Diegoapp55/Proyecto-Sistemas-Embebidos-Smash-Rows/Esquematicos/ESP32/Smash Rows Back.png

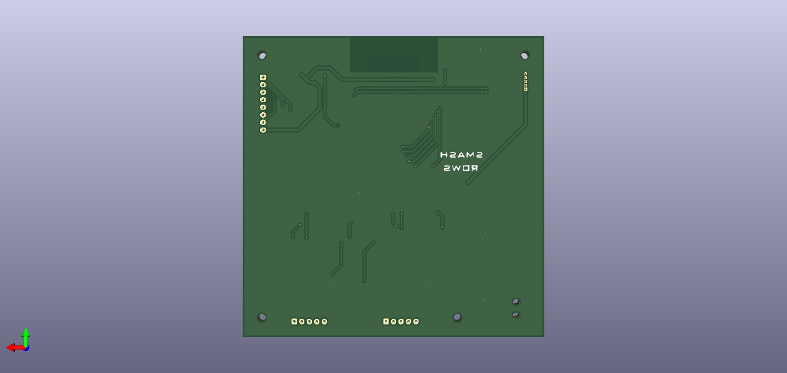
Esquematicos/ESP32/Smash Rows Back.png
