Diegoapp55/Proyecto-Sistemas-Embebidos-Smash-Rows/Imagenes/App_Image/AcercaDe.png

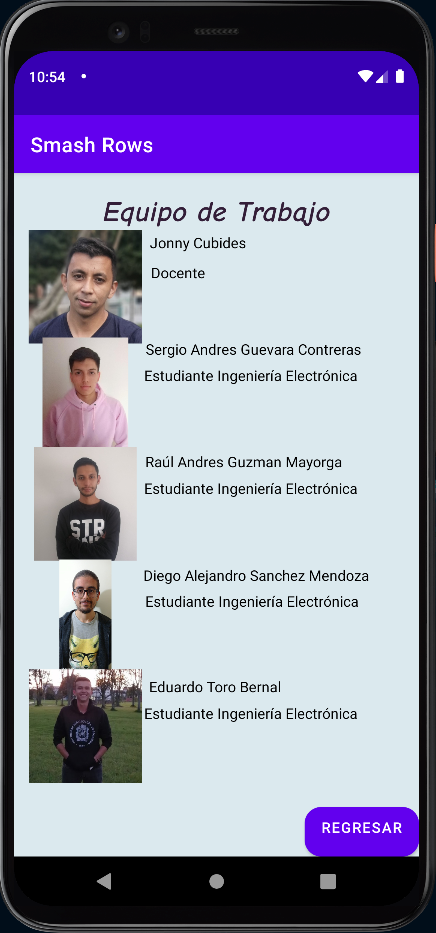
Imagenes/App_Image/AcercaDe.png
