Diegoapp55/Proyecto-Sistemas-Embebidos-Smash-Rows/Imagenes/App_Image/BaseDatos.png

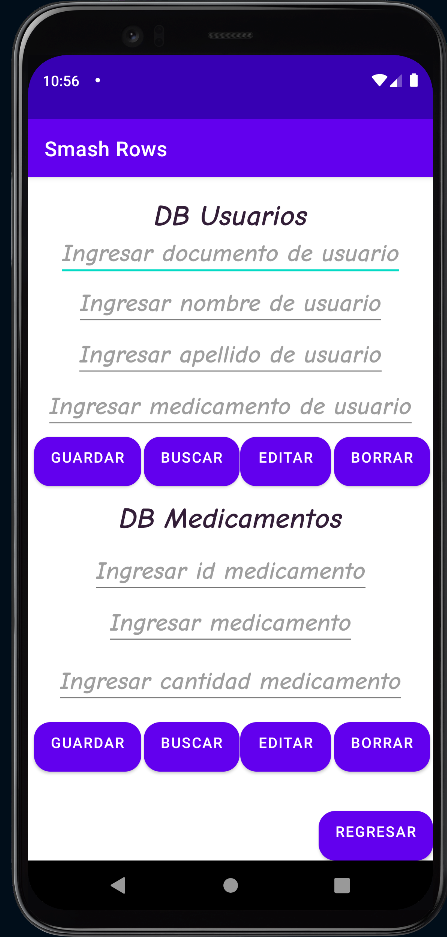
Imagenes/App_Image/BaseDatos.png
