Diegoapp55/Proyecto-Sistemas-Embebidos-Smash-Rows/Imagenes/App_Image/EscanearDocumento.png

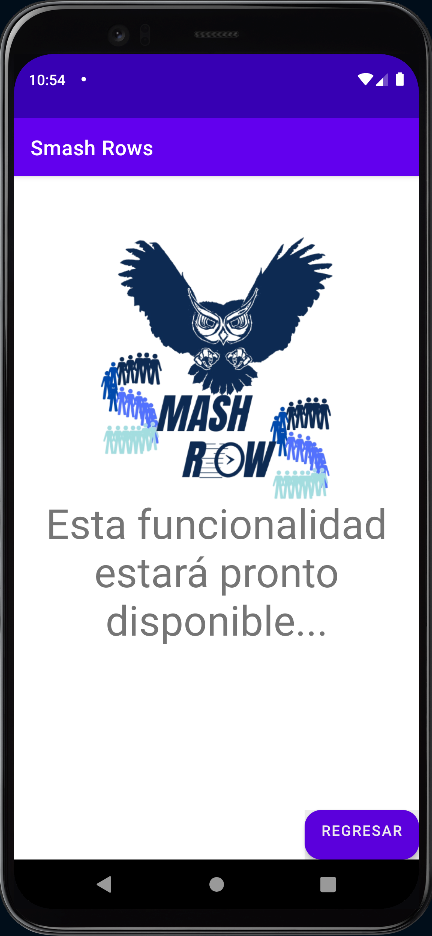
Imagenes/App_Image/EscanearDocumento.png
