Diegoapp55/Proyecto-Sistemas-Embebidos-Smash-Rows/Imagenes/App_Image/Insertar_Documento.png

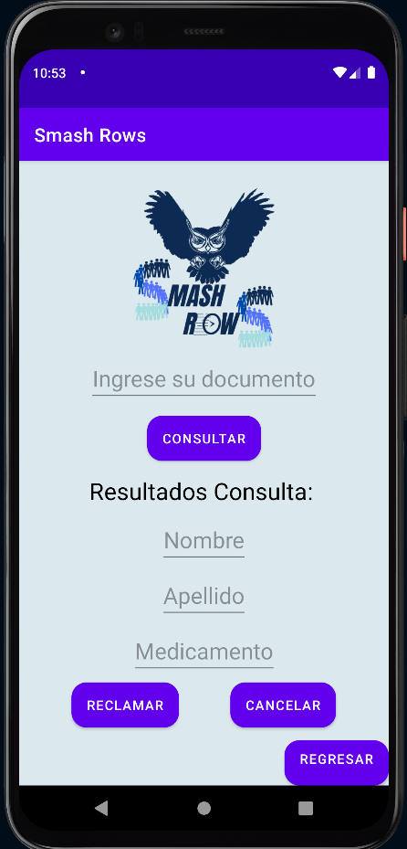
Imagenes/App_Image/Insertar_Documento.png
