Diegoapp55/Proyecto-Sistemas-Embebidos-Smash-Rows/Imagenes/App_Image/Interfaz_Principal.png

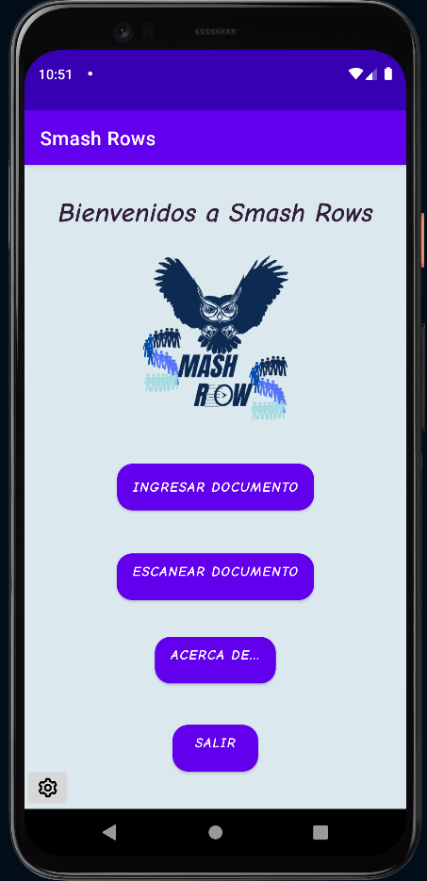
Imagenes/App_Image/Interfaz_Principal.png
