Diegoapp55/Proyecto-Sistemas-Embebidos-Smash-Rows/Imagenes/caaaaja.jpeg

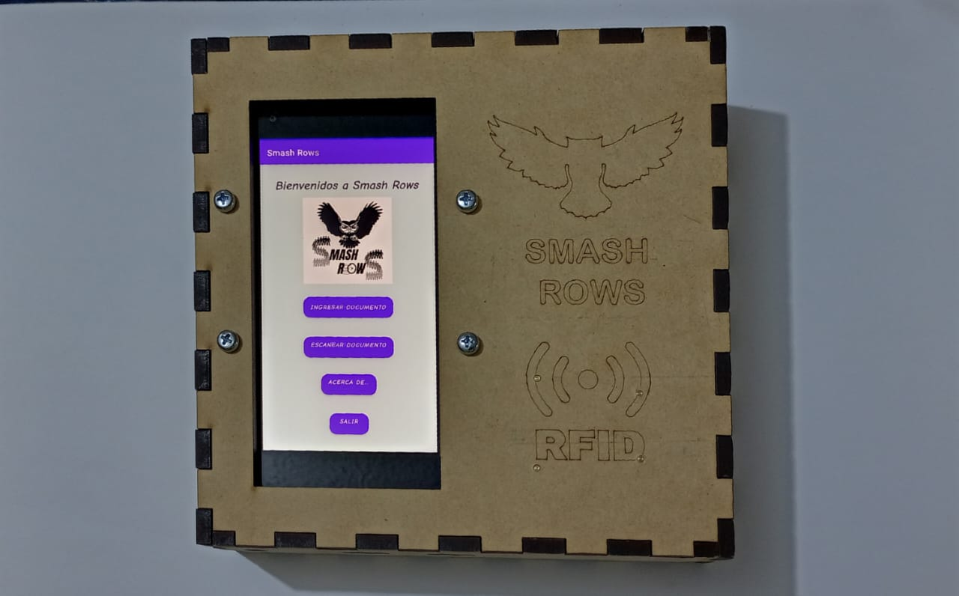
Imagenes/caaaaja.jpeg
