Diegoapp55/Proyecto-Sistemas-Embebidos-Smash-Rows/Imagenes/caja_bosquejo.jpeg

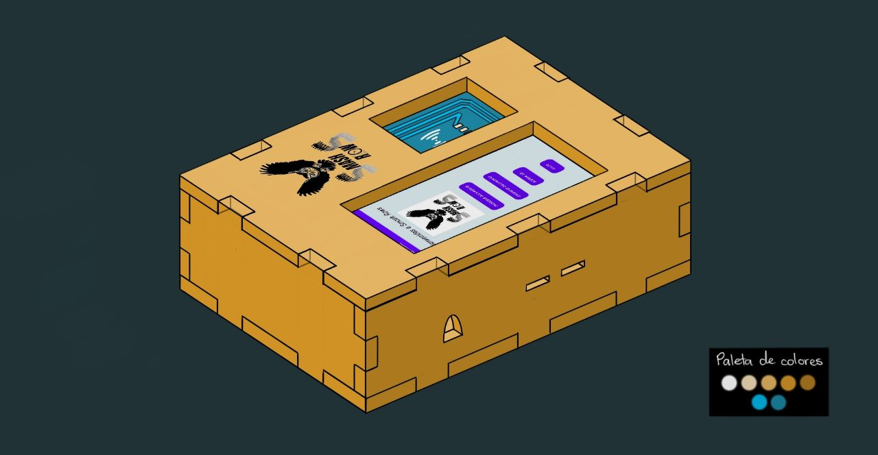
Imagenes/caja_bosquejo.jpeg
