Diegoapp55/Proyecto-Sistemas-Embebidos-Smash-Rows/Imagenes/cajaautocad.png

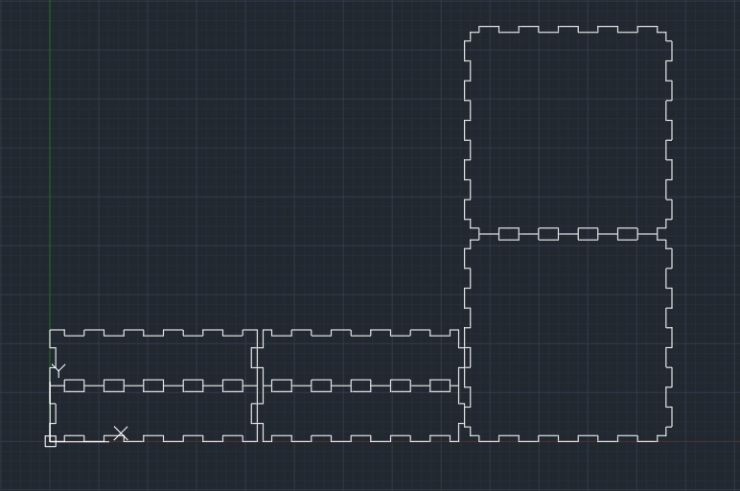
Imagenes/cajaautocad.png
