Diegoapp55/Proyecto-Sistemas-Embebidos-Smash-Rows/Imagenes/ESP32_Blocks.png

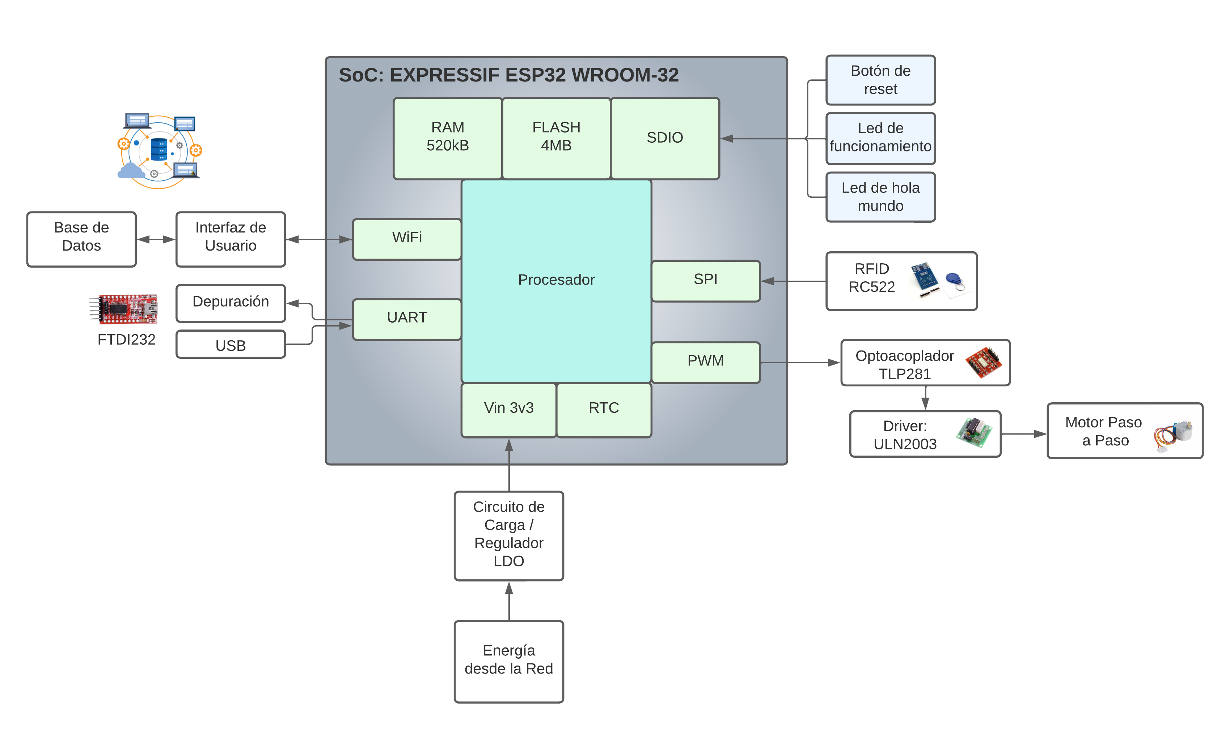
Imagenes/ESP32_Blocks.png
