Diegoapp55/Proyecto-Sistemas-Embebidos-Smash-Rows/Imagenes/Esquemático_SE/esquematico_bloques.png

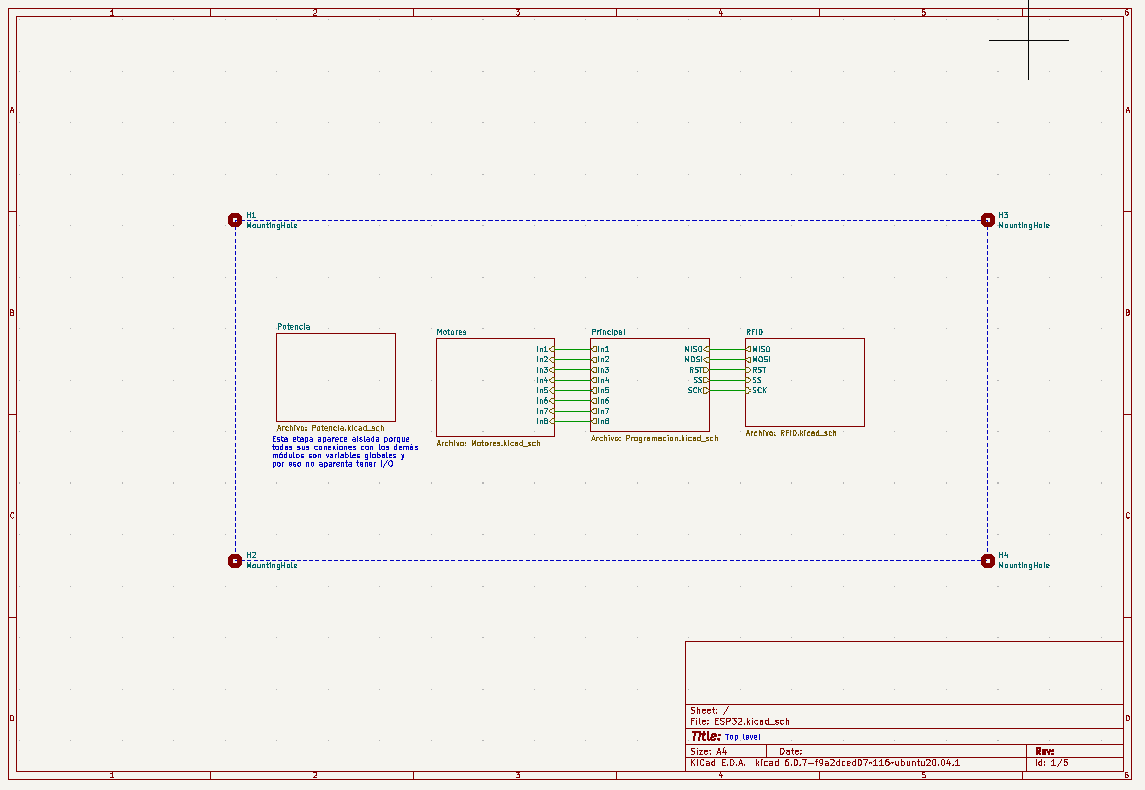
Imagenes/Esquemático_SE/esquematico_bloques.png
