Diegoapp55/Proyecto-Sistemas-Embebidos-Smash-Rows/Imagenes/Esquemático_SE/motores_esquematico.png

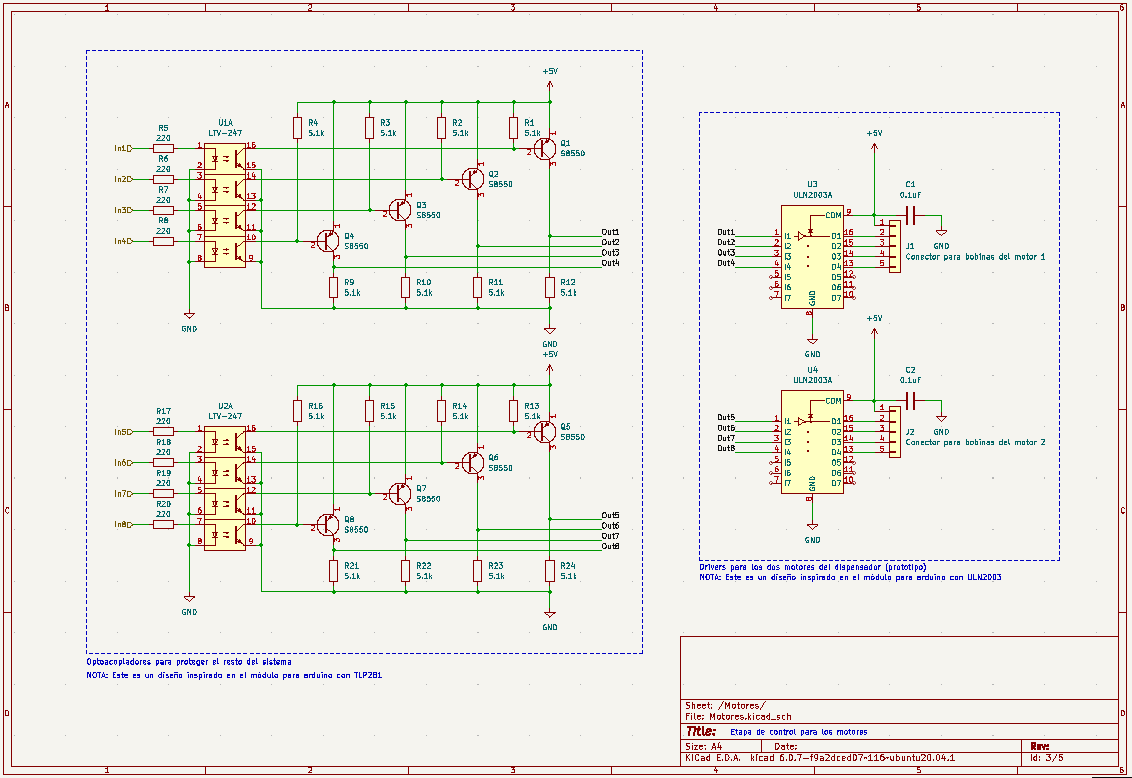
Imagenes/Esquemático_SE/motores_esquematico.png
