Diegoapp55/Proyecto-Sistemas-Embebidos-Smash-Rows/Imagenes/Esquemático_SE/potencia_esquematico.png

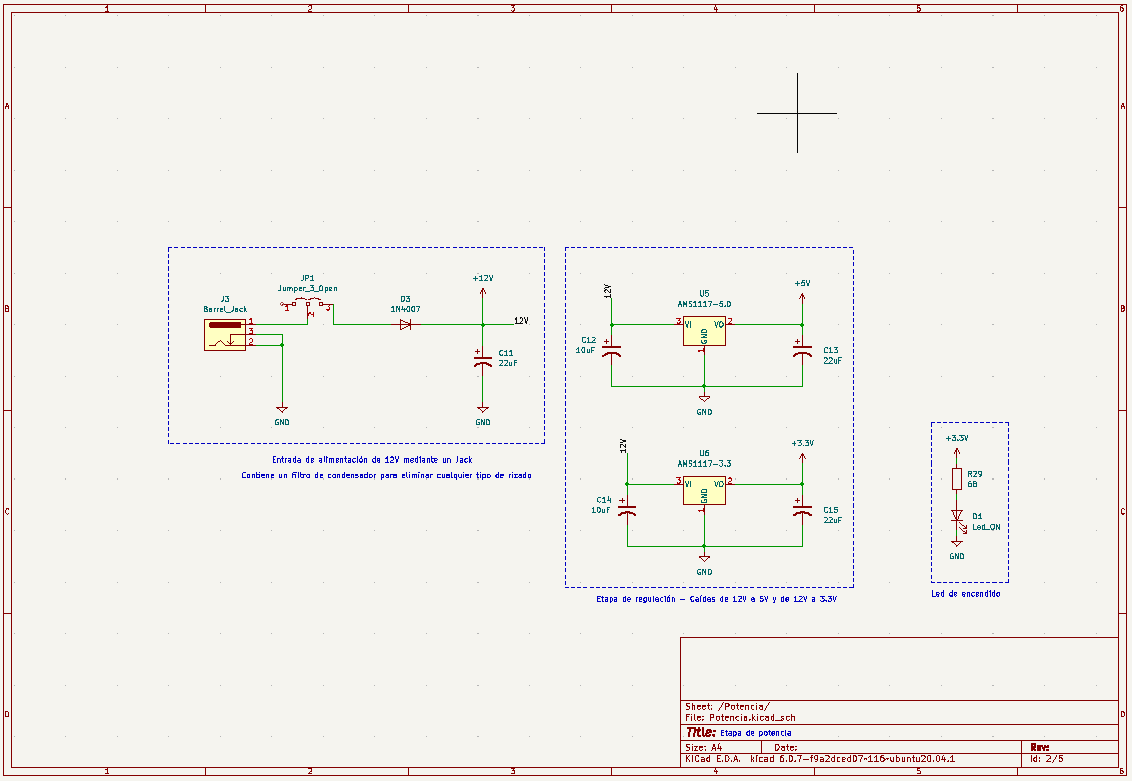
Imagenes/Esquemático_SE/potencia_esquematico.png
