Diegoapp55/Proyecto-Sistemas-Embebidos-Smash-Rows/Imagenes/Esquemático_SE/programacion_esquematico.png

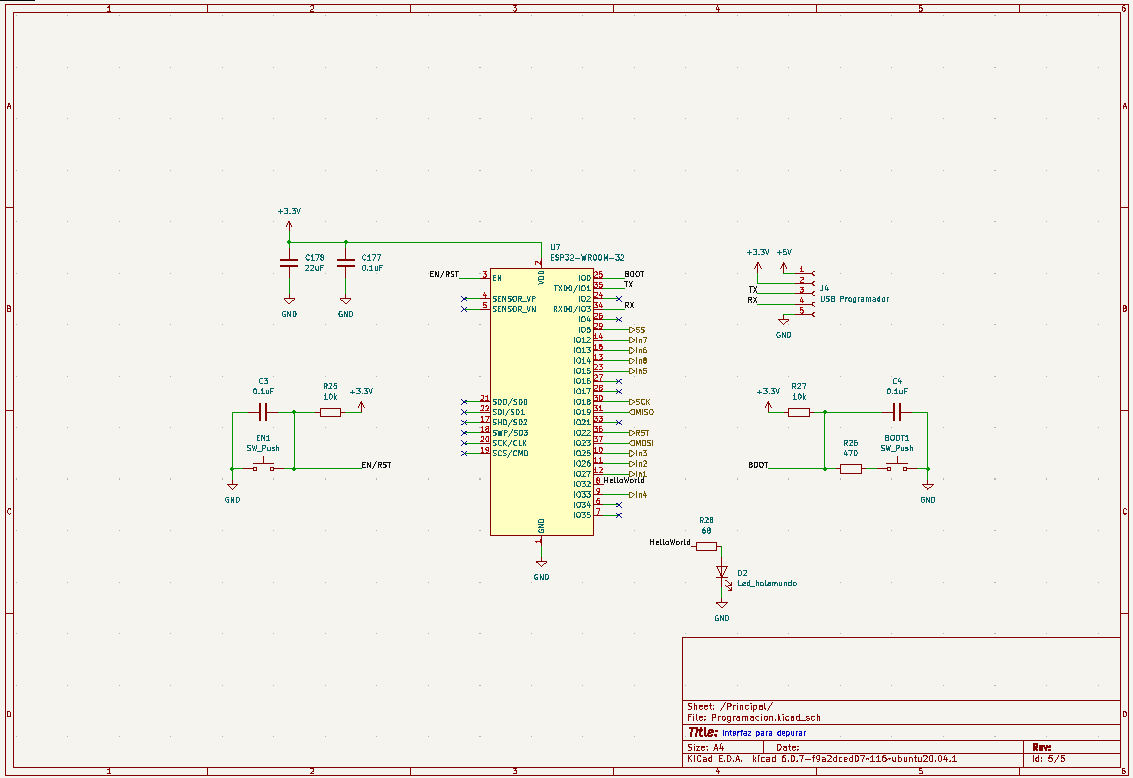
Imagenes/Esquemático_SE/programacion_esquematico.png
