Diegoapp55/Proyecto-Sistemas-Embebidos-Smash-Rows/Imagenes/Esquemático_SE/RFID_esquematico.png

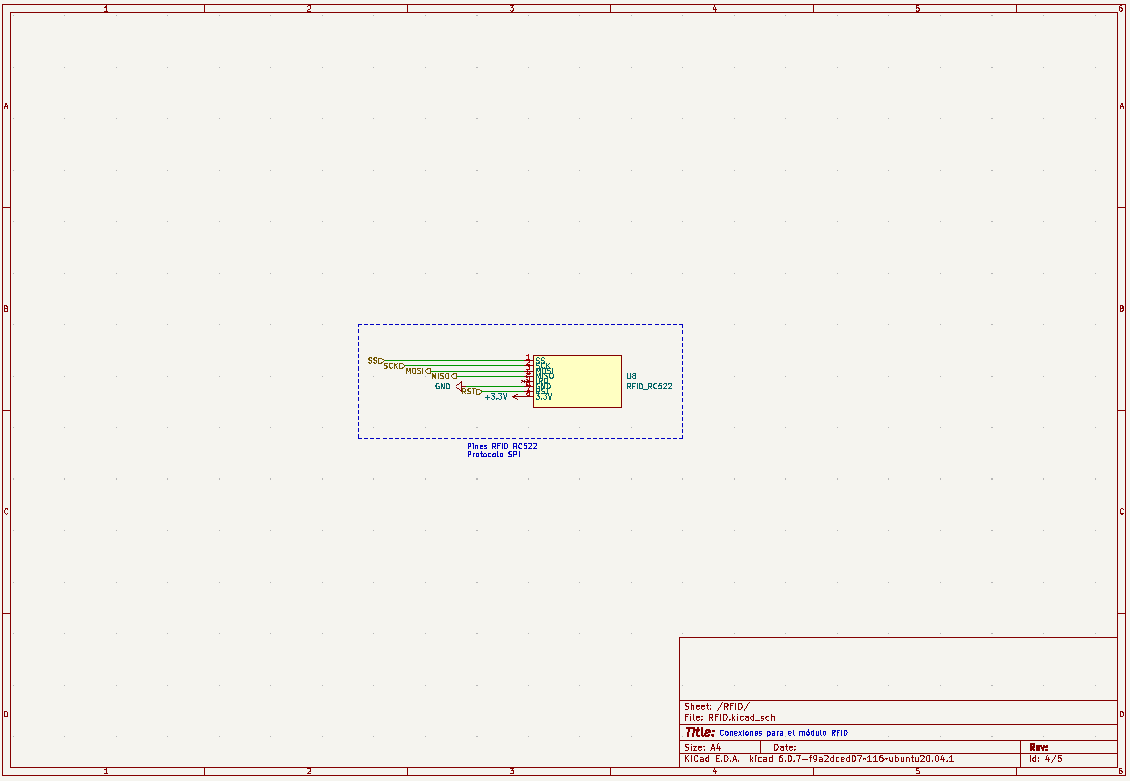
Imagenes/Esquemático_SE/RFID_esquematico.png
