Diegoapp55/Proyecto-Sistemas-Embebidos-Smash-Rows/Imagenes/Illustrator.png

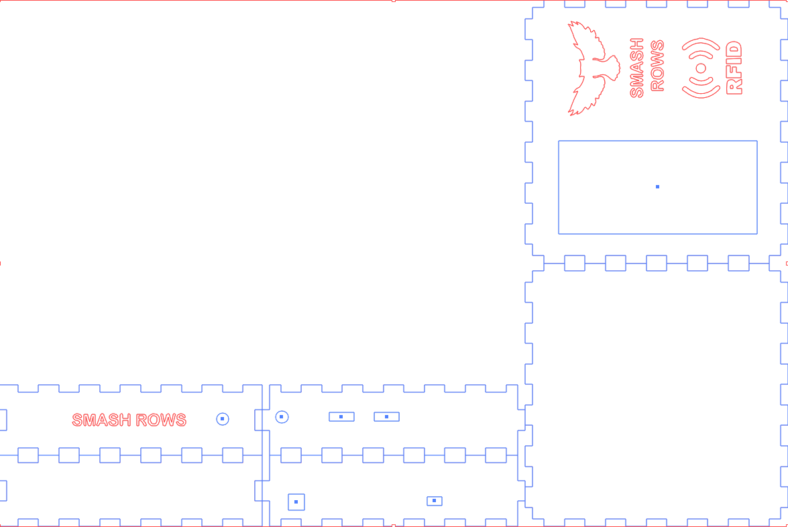
Imagenes/Illustrator.png
