Diegoapp55/Proyecto-Sistemas-Embebidos-Smash-Rows/Imagenes/lista_compras.png

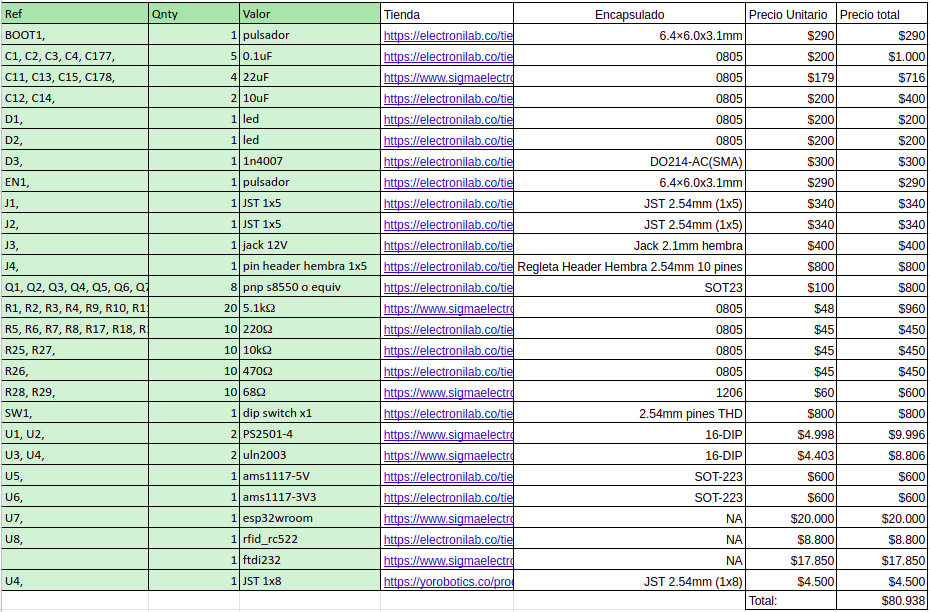
Imagenes/lista_compras.png
