Diegoapp55/Proyecto-Sistemas-Embebidos-Smash-Rows/Imagenes/MASH 2.png

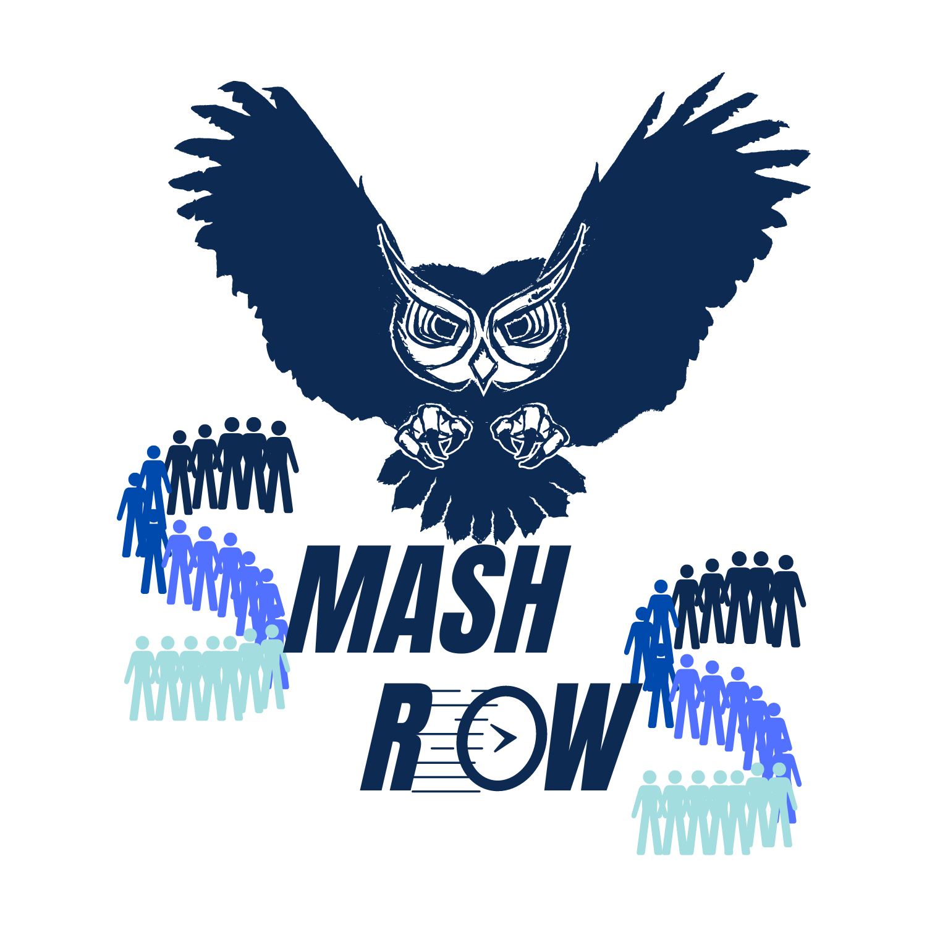
Imagenes/MASH 2.png
