Diegoapp55/Proyecto-Sistemas-Embebidos-Smash-Rows/Imagenes/MASH-removebg-preview.png

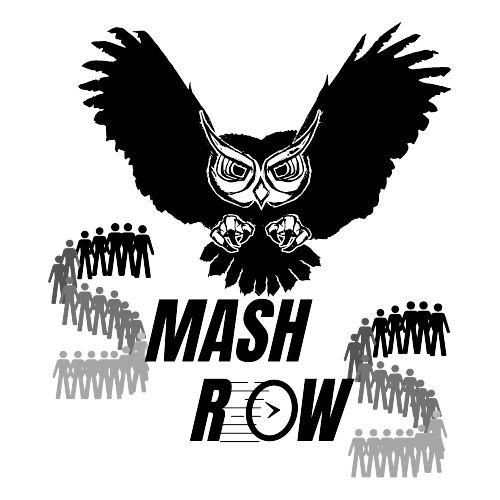
Imagenes/MASH-removebg-preview.png
