Diegoapp55/Proyecto-Sistemas-Embebidos-Smash-Rows/Imagenes/pcb_frontal.jpg

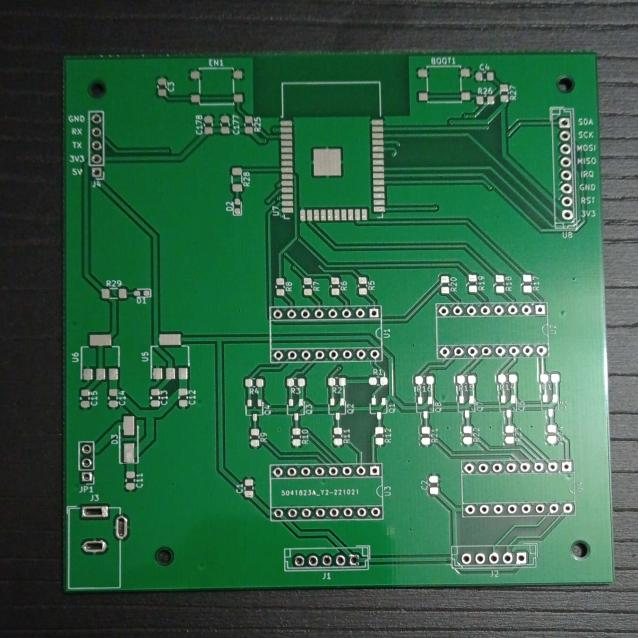
Imagenes/pcb_frontal.jpg
