Diegoapp55/Proyecto-Sistemas-Embebidos-Smash-Rows/Imagenes/pcb_trasera.jpg

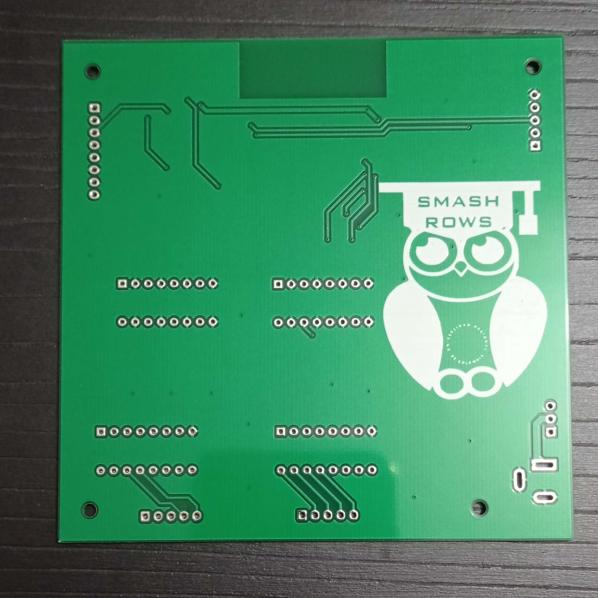
Imagenes/pcb_trasera.jpg
