Diegoapp55/Proyecto-Sistemas-Embebidos-Smash-Rows/Imagenes/placa_soldada.png

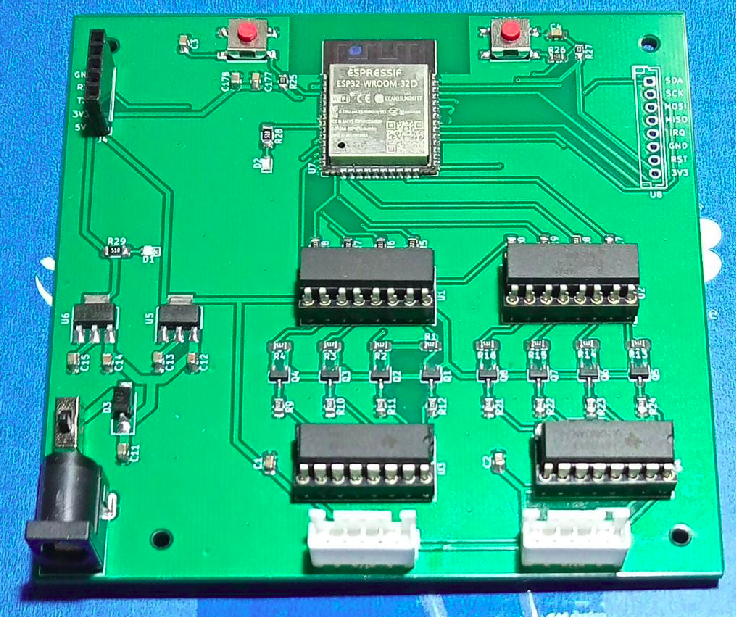
Imagenes/placa_soldada.png
