Diegoapp55/Proyecto-Sistemas-Embebidos-Smash-Rows/Imagenes/Ruteo/B_Cu.png

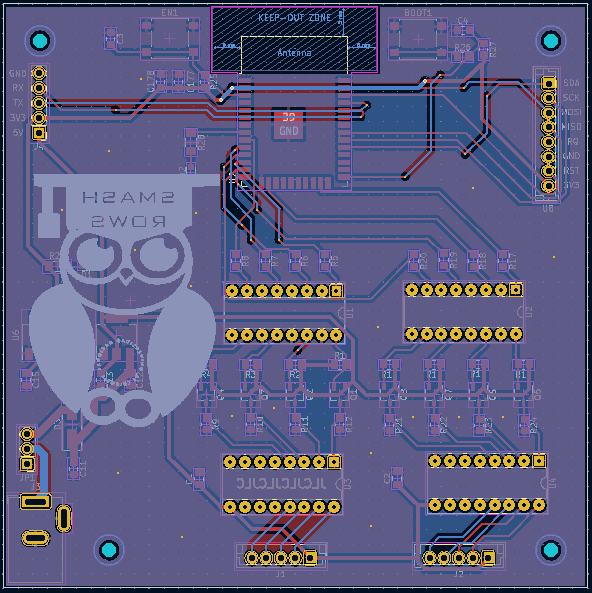
Imagenes/Ruteo/B_Cu.png
