Diegoapp55/Proyecto-Sistemas-Embebidos-Smash-Rows/Imagenes/Ruteo/F_Cu.png

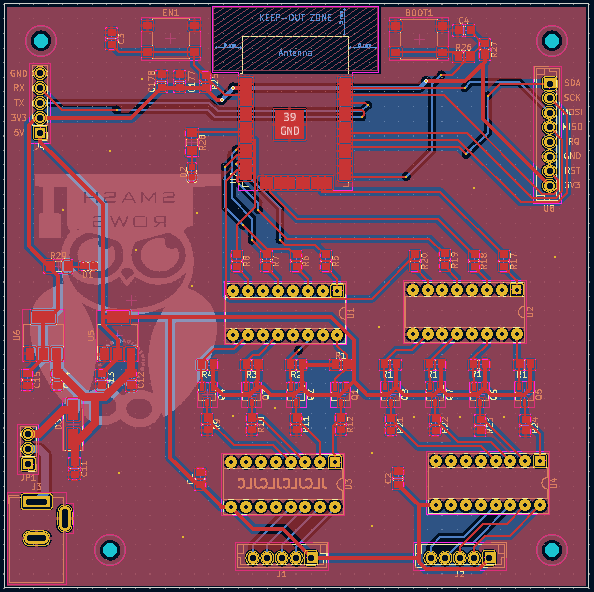
Imagenes/Ruteo/F_Cu.png
