Diegoapp55/Proyecto-Sistemas-Embebidos-Smash-Rows/Imagenes/SE Smash_Rows.png

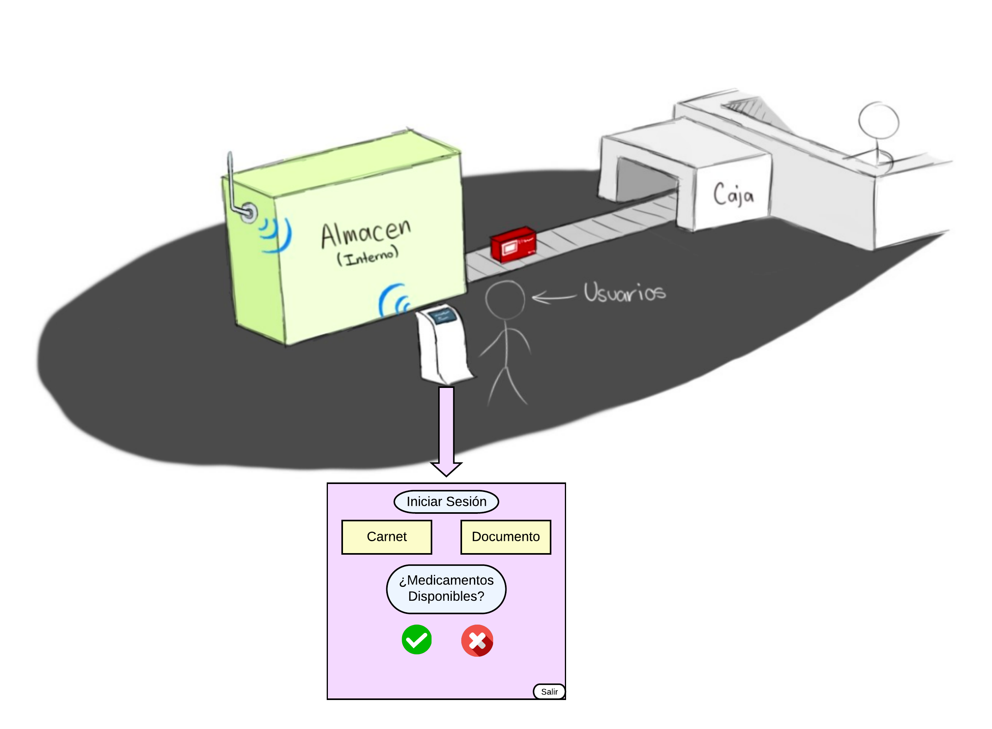
Imagenes/SE Smash_Rows.png
