Diegoapp55/Proyecto-Sistemas-Embebidos-Smash-Rows/Imagenes/Smash Rows - Sistemas Embebidos.png

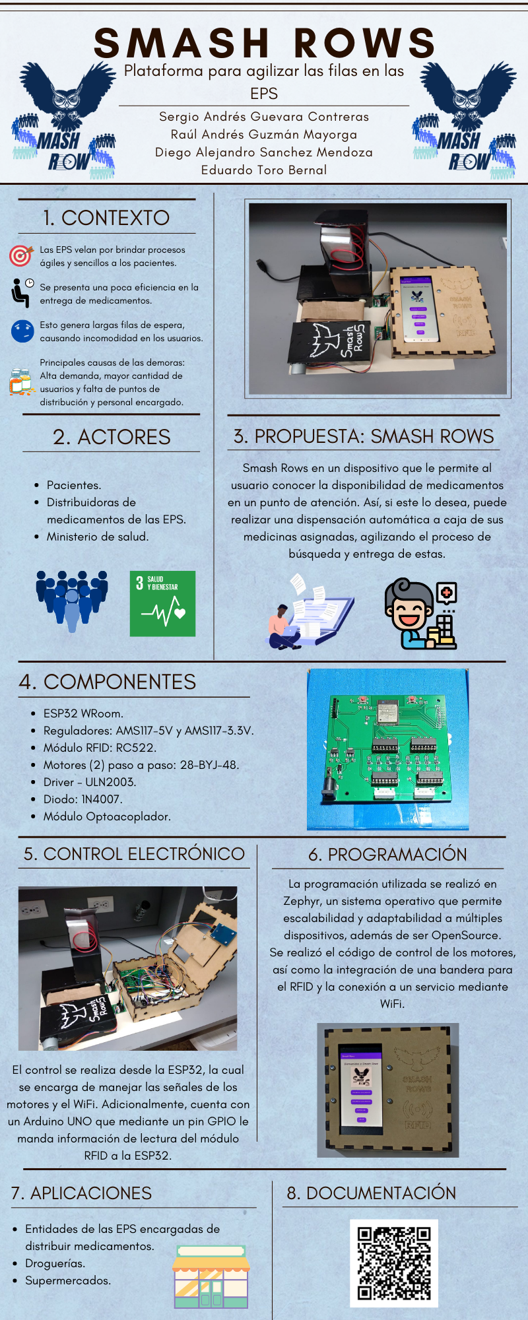
Imagenes/Smash Rows - Sistemas Embebidos.png
