Diegoapp55/Proyecto-Sistemas-Embebidos-Smash-Rows/Imagenes/Visor.png

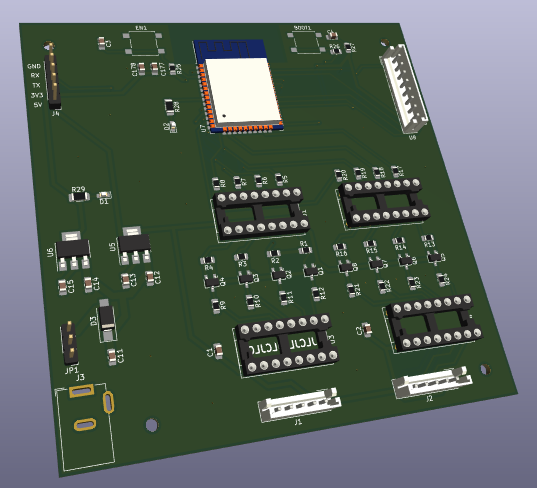
Imagenes/Visor.png
