Diegoapp55/Proyecto-Sistemas-Embebidos-Smash-Rows/Zephyr/img/codelite-build-opt.png

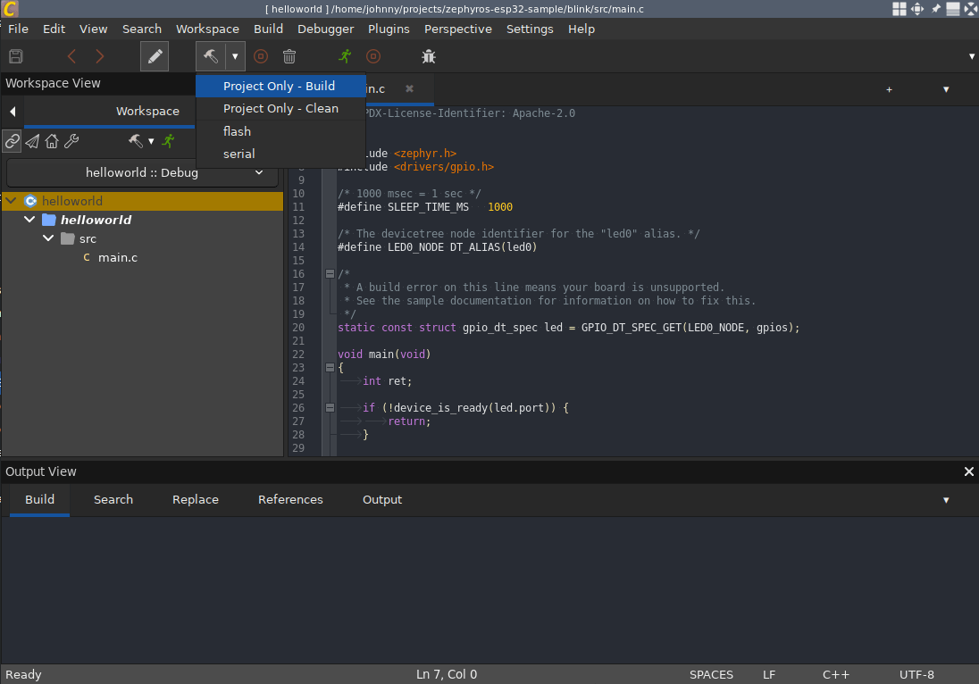
Zephyr/img/codelite-build-opt.png
