Diegoapp55/Proyecto-Sistemas-Embebidos-Smash-Rows/Zephyr/img/geany-build-project.png

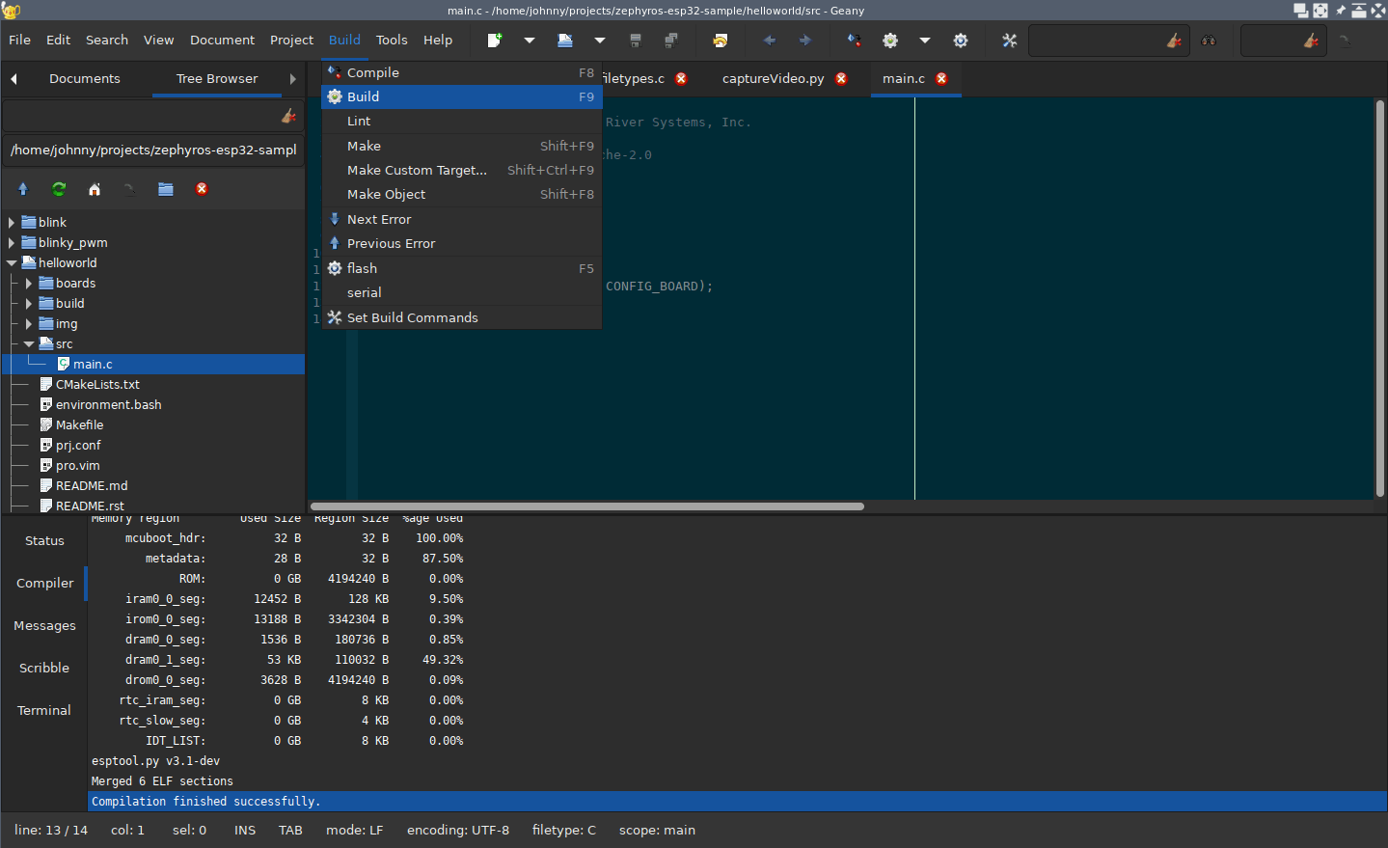
Zephyr/img/geany-build-project.png
