Diegoapp55/Proyecto-Sistemas-Embebidos-Smash-Rows/Zephyr/img/geany-set-build-commands.png

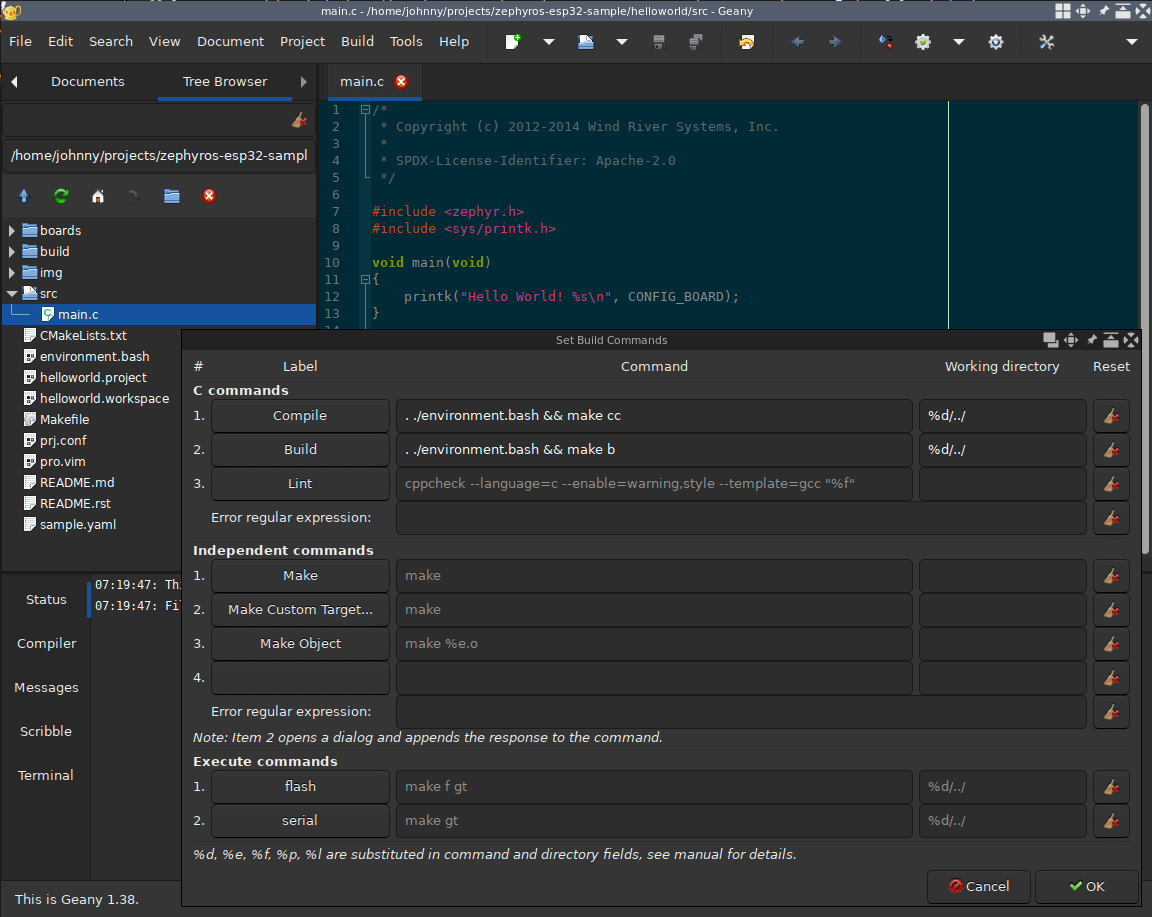
Zephyr/img/geany-set-build-commands.png
