Diegoapp55/Proyecto-Sistemas-Embebidos-Smash-Rows/Esquematicos-KiCad/Smash-Rows/Smash-Rows.kicad_sch

## KiCad design Esquematicos-KiCad/Smash-Rows/Smash-Rows.kicad_sch (2022-09-13)

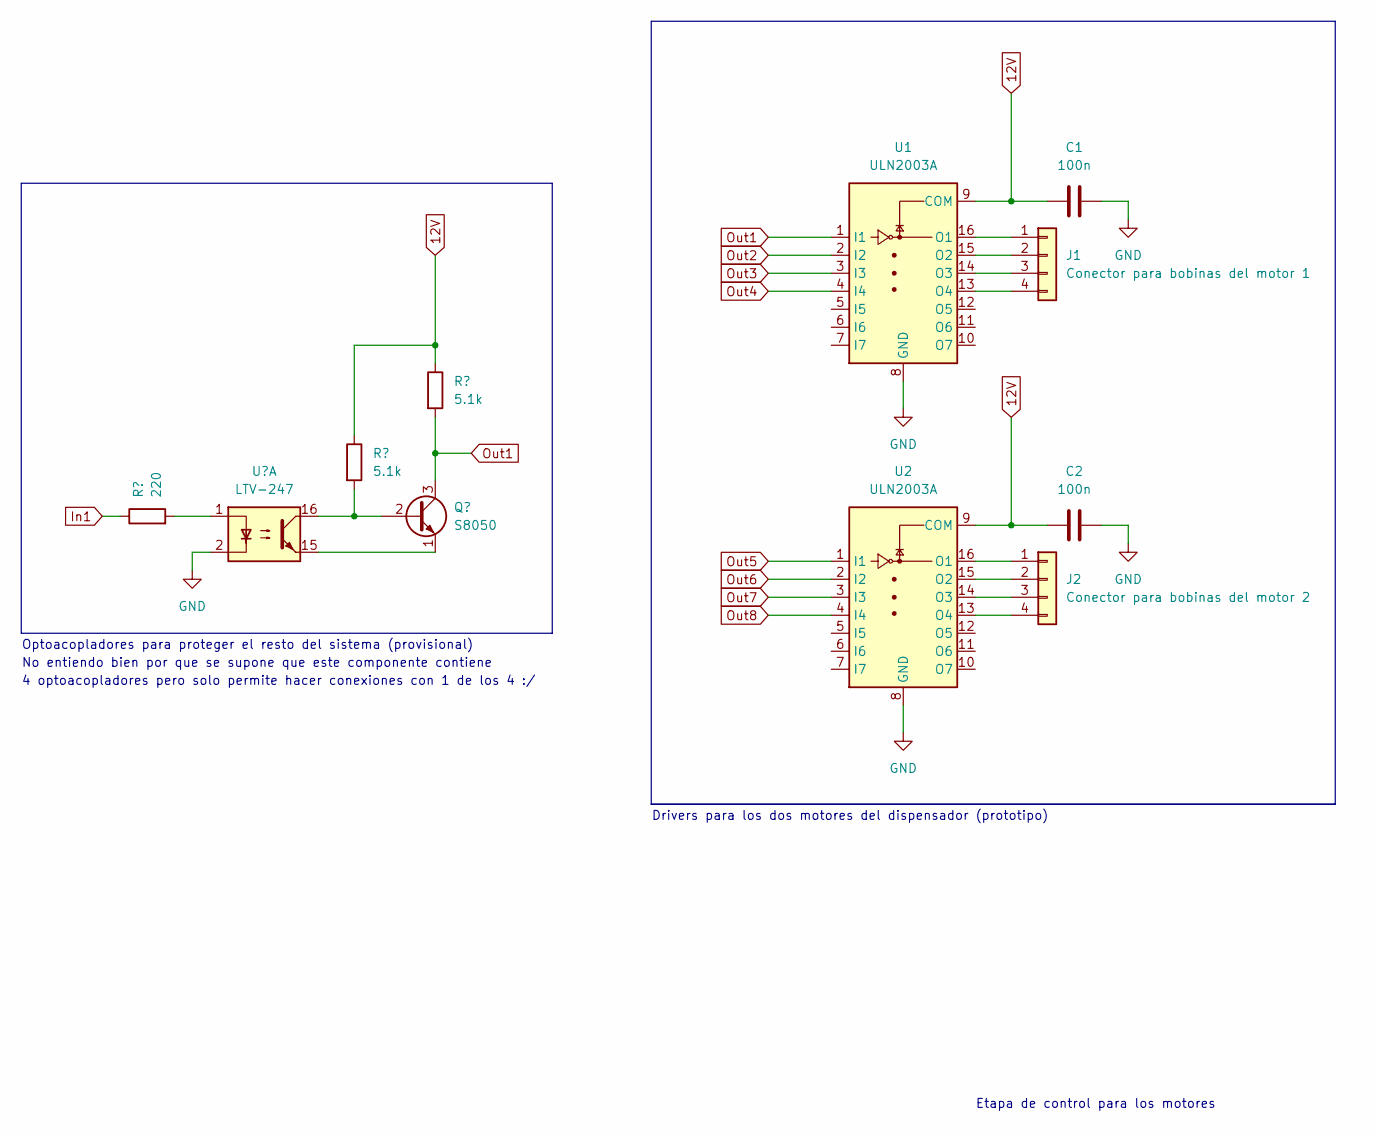
[picture p47: schematic Smash-Rows.kicad_sch]

Parts:
C1, C2: 100n
J1: Conector para bobinas del motor 1
J2: Conector para bobinas del motor 2
U1, U2: ULN2003A

Connections:
12V: C1.1, C2.1, U1.9 (COM), U2.9 (COM)
unnamed: J1.1, U1.16 (O1)
unnamed: J1.2, U1.15 (O2)
unnamed: J1.3, U1.14 (O3)
unnamed: J1.4, U1.13 (O4)
unnamed: J2.1, U2.16 (O1)
unnamed: J2.2, U2.15 (O2)
unnamed: J2.3, U2.14 (O3)
unnamed: J2.4, U2.13 (O4)
Out1: U1.1 (I1)
Out2: U1.2 (I2)
Out3: U1.3 (I3)
Out4: U1.4 (I4)
Out5: U2.1 (I1)
Out6: U2.2 (I2)
Out7: U2.3 (I3)
Out8: U2.4 (I4)

Notes on the sheet:
Drivers para los dos motores del dispensador (prototipo)
Etapa de control para los motores
4 optoacopladores pero solo permite hacer conexiones con 1 de los 4 :/
Optoacopladores para proteger el resto del sistema (provisional)
No entiendo bien por que se supone que este componente contiene
