Diegoapp55/Proyecto-Sistemas-Embebidos-Smash-Rows/Zephyr/blink/src/main.c

/*
 * Copyright (c) 2016 Intel Corporation
 *
 * SPDX-License-Identifier: Apache-2.0
 */

#include <zephyr/kernel.h>
#include <zephyr/drivers/gpio.h>
#include <esp_log.h>

/* 1000 msec = 1 sec */
#define SLEEP_TIME_MS   1000

/* The devicetree node identifier for the "led0" alias. */
#define LED0_NODE DT_ALIAS(led0)
#define LED2_NODE DT_ALIAS(led2)

/*
 * A build error on this line means your board is unsupported.
 * See the sample documentation for information on how to fix this.
 */
static const struct gpio_dt_spec led = GPIO_DT_SPEC_GET(LED0_NODE, gpios);
static const struct gpio_dt_spec led2 = GPIO_DT_SPEC_GET(LED2_NODE, gpios);

void main(void)
{
	int ret;

	if (!device_is_ready(led.port)) {
		return;
	}

	ret = gpio_pin_configure_dt(&led, GPIO_OUTPUT_ACTIVE);
	if (ret < 0) {
		return;
	}

	if (!device_is_ready(led2.port)) {
		return;
	}

	ret = gpio_pin_configure_dt(&led2, GPIO_OUTPUT_ACTIVE);
	if (ret < 0) {
		return;
	}

	while (1) {
		ret = gpio_pin_toggle_dt(&led);
		if (ret < 0) {
			return;
		}
		ret = gpio_pin_toggle_dt(&led2);
		if (ret < 0) {
			return;
		}
		k_msleep(SLEEP_TIME_MS);
	}
}
