Diegoapp55/Proyecto-Sistemas-Embebidos-Smash-Rows/Zephyr/PruebaESP32/src/main.c

/*
 * Copyright (c) 2012-2014 Wind River Systems, Inc.
 *
 * SPDX-License-Identifier: Apache-2.0
 */

#include <zephyr/kernel.h>
#include <zephyr/drivers/gpio.h>
#include <esp_log.h>
#include <zephyr/sys/printk.h>

/* 1000 msec = 1 sec */
#define SLEEP_TIME_MS   3000

/* The devicetree node identifier for the "led0" alias. */
#define LED0_NODE DT_ALIAS(led0)

static const struct gpio_dt_spec led = GPIO_DT_SPEC_GET(LED0_NODE, gpios);

void main(void)
{
	printk("Hello World! %s\n", CONFIG_BOARD);
	int ret;

	if (!device_is_ready(led.port)) {
		return;
	}

	ret = gpio_pin_configure_dt(&led, GPIO_OUTPUT_ACTIVE);
	if (ret < 0) {
		return;
	}

	while (1) {
		ret = gpio_pin_toggle_dt(&led);
		if (ret < 0) {
			return;
		}
		k_msleep(SLEEP_TIME_MS);
	}
}
